deanm1278/bottomfeeder/synthqp/src/waveDefs.cpp

#include "waveDefs.h"
const char *waveforms[] = {
 "wav00.w",
 "wav01.w",
 "wav02.w",
 "wav03.w",
 "wav04.w",
 "wav05.w",
 "wav06.w",
 "wav07.w",
 "wav08.w",
 "wav09.w",
 "wav10.w",
 "wav11.w",
 "wav12.w",
 "wav13.w",
 "wav14.w",
 "wav15.w",
 "wav16.w",
 "wav17.w",
 "wav18.w",
 "wav19.w",
 "wav20.w",
 "wav21.w",
 "wav22.w",
 "wav23.w",
 "wav24.w",
 "wav25.w",
 "wav26.w",
 "wav27.w",
 "wav28.w",
 "wav29.w",
 "wav30.w",
 "wav31.w",
 "wav32.w",
 "wav33.w",
 "wav34.w",
 "wav35.w",
 "wav36.w",
 "wav37.w",
 "wav38.w",
 "wav39.w",
 "wav40.w",
 "wav41.w",
 "wav42.w",
 "wav43.w",
 "wav44.w",
 "wav45.w",
 "wav46.w",
 "wav47.w",
 "wav48.w",
 "wav49.w",
 "wav50.w",
 "wav51.w",
 "wav52.w",
 "wav53.w",
 "wav54.w",
 "wav55.w",
 "wav56.w",
 "wav57.w",
 "wav58.w",
 "wav59.w",
 "wav60.w",
 "wav61.w",
 "wav62.w",
 "wav63.w",
 "wav64.w",
 "wav65.w",
 "wav66.w",
 "wav67.w",
 "wav68.w",
 "wav69.w",
 "wav70.w",
 "wav71.w",
 "wav72.w",
 "wav73.w",
 "wav74.w",
 "wav75.w",
 "wav76.w",
 "wav77.w",
 "wav78.w",
 "wav79.w",
 "wav80.w",
 "wav81.w",
 "wav82.w",
 "wav83.w",
 "wav84.w",
 "wav85.w",
 "wav86.w",
 "wav87.w",
 "wav88.w",
 "wav89.w",
 "wav90.w",
 "wav91.w",
 "wav92.w",
 "wav93.w",
 "wav94.w",
 "wav95.w",
 "wav96.w",
 "wav97.w",
 "wav98.w",
 "wav99.w",
 "wav100.w",
 "wav101.w",
 "wav102.w",
 "wav103.w",
 "wav104.w",
 "wav105.w",
 "wav106.w",
 "wav107.w",
 "wav108.w",
 "wav109.w",
 "wav110.w",
 "wav111.w",
 "wav112.w",
 "wav113.w",
 "wav114.w",
 "wav115.w",
 "wav116.w",
 "wav117.w",
 "wav118.w",
 "wav119.w",
 "wav120.w",
 "wav121.w",
 "wav122.w",
 "wav123.w",
 "wav124.w",
 "wav125.w",
 "wav126.w",
 "wav127.w"
};
